liorgonnen/kinetikeys-chorder/firmware/include/BLECentralConnection.h

#ifndef BLECENTRALCONNECTION_H
#define BLECENTRALCONNECTION_H

#include "BLEConnectionAdapter.h"

typedef void (*SlaveInputReceivedCallback) (uint8_t input);

// GATT Server
// A peripheral can advertise to let other device know it's there, but
// It's the Cetnral that actually sends the connection request
class BLECentralConnection : public BLEConnectionAdapter
{
public:
    void setup();
    bool isSlaveConnected();
    void setOnInputReceivedCallback(SlaveInputReceivedCallback callback);

private:
    // TODO: Need to check if I can use std::funcrtion in Arduino code
    static void onScanResponse(ble_gap_evt_adv_report_t* report);
    static void onDeviceConnected(uint16_t connectionHandle);
    static void onDeviceDisconnected(uint16_t connectionHandle, uint8_t reason);
    static void onSlaveInputReceived(BLEClientUart& service);

    static BLEClientBas  slaveBatteryService;
    static BLEClientDis  slaveDeviceInfoService;
    static BLEClientUart slaveUartService;

    static SlaveInputReceivedCallback slaveInputReceivedCallback;
};

#endif
